EduardsBaumanis/spele/site-assets/pdf-pages/guide-01.png

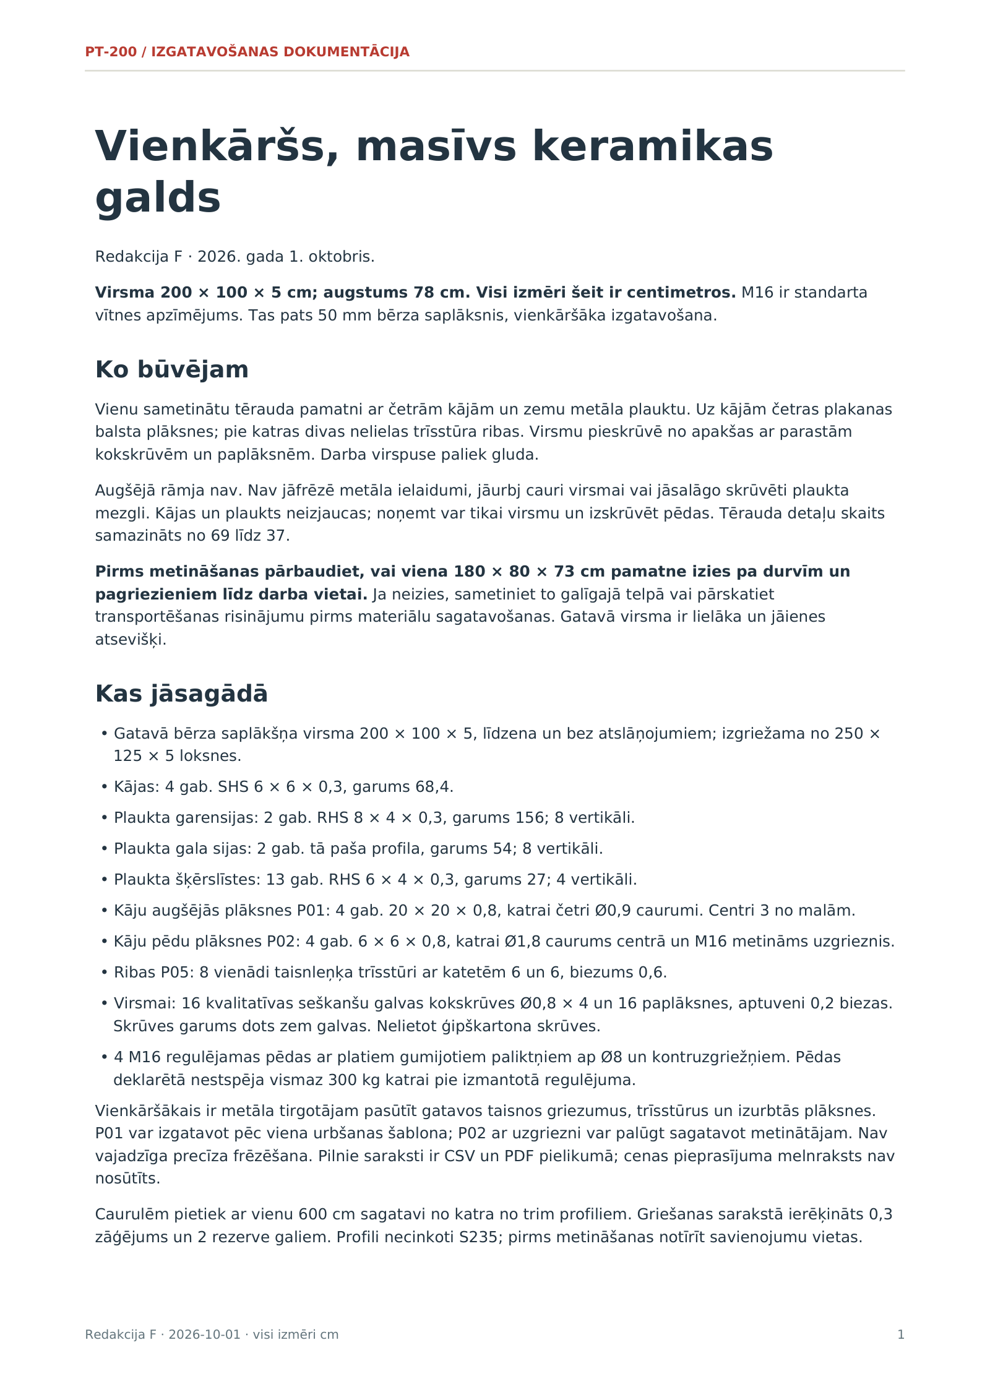
site-assets/pdf-pages/guide-01.png
