EduardsBaumanis/spele/site-assets/pdf-pages/guide-02.png

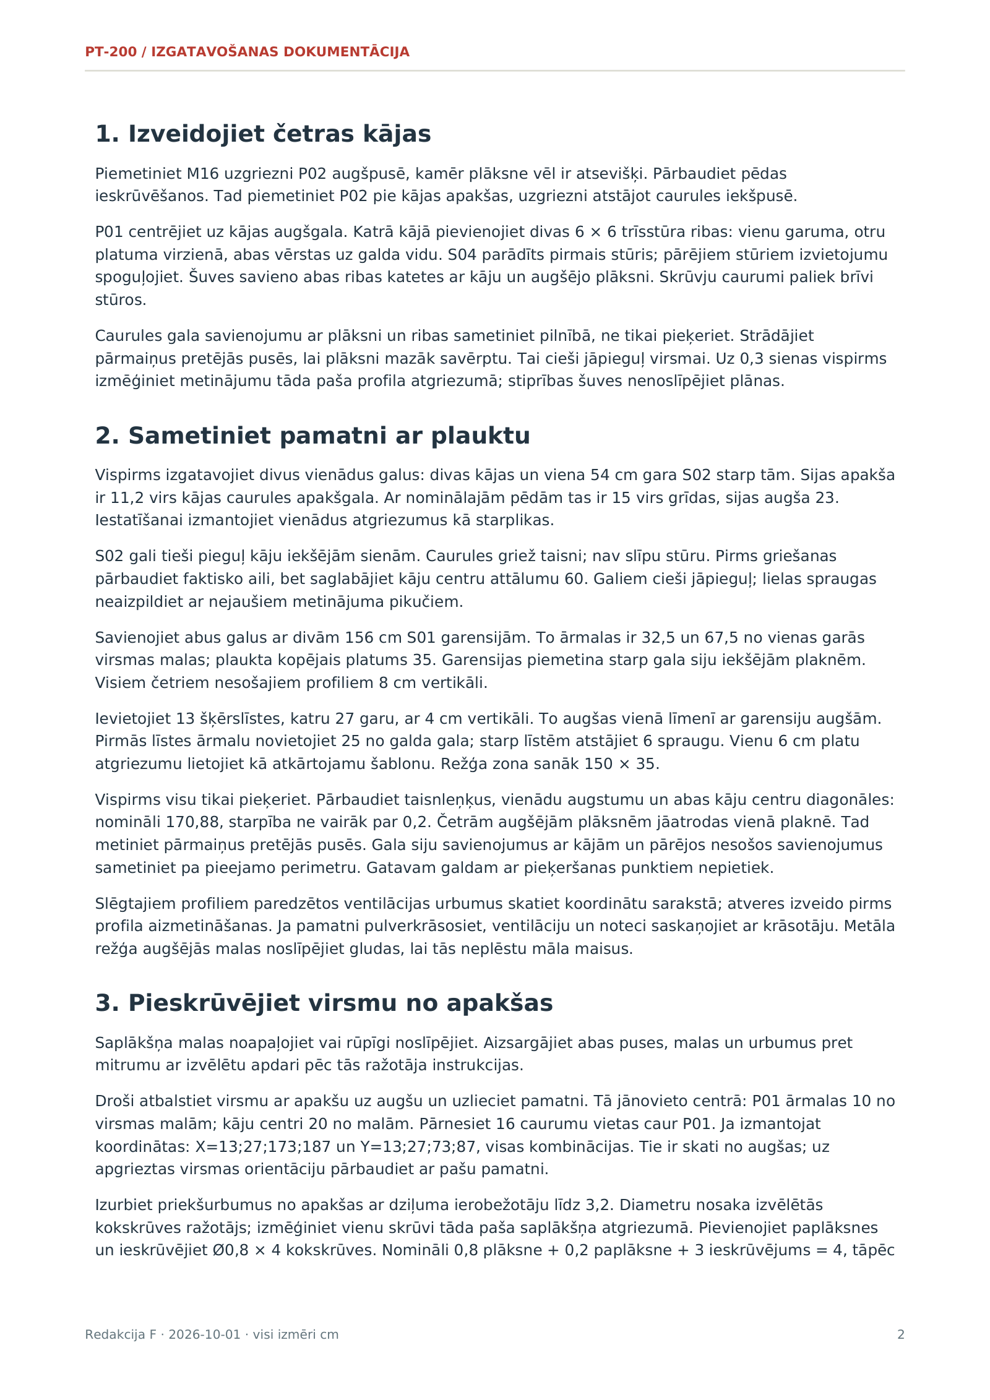
site-assets/pdf-pages/guide-02.png
