EduardsBaumanis/spele/site-assets/pdf-pages/guide-06.png

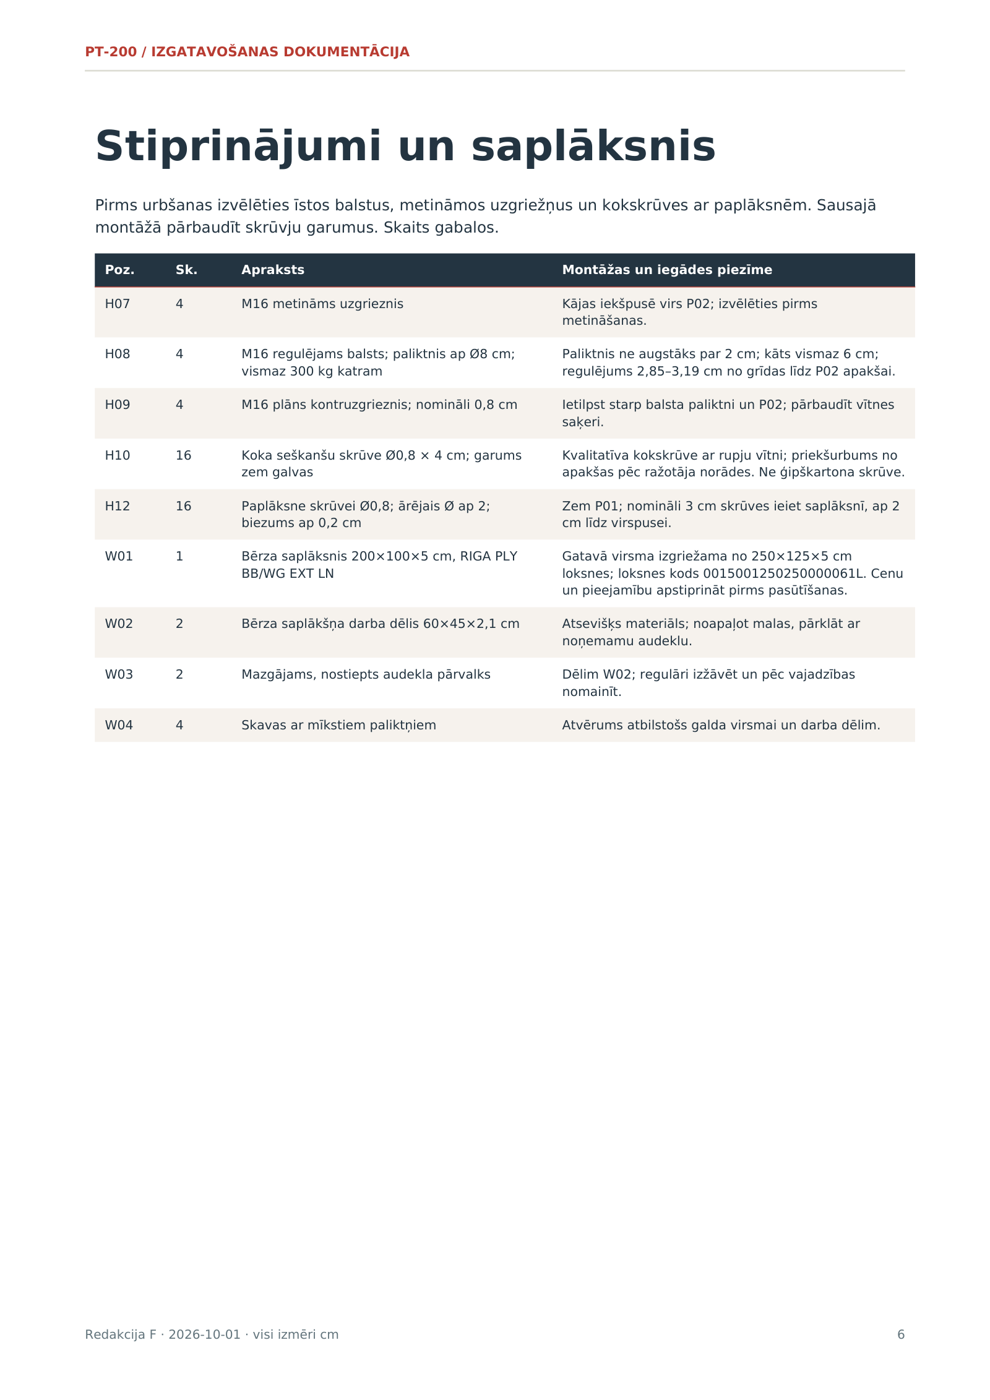
site-assets/pdf-pages/guide-06.png
