EduardsBaumanis/spele/site-assets/pdf-pages/guide-08.png

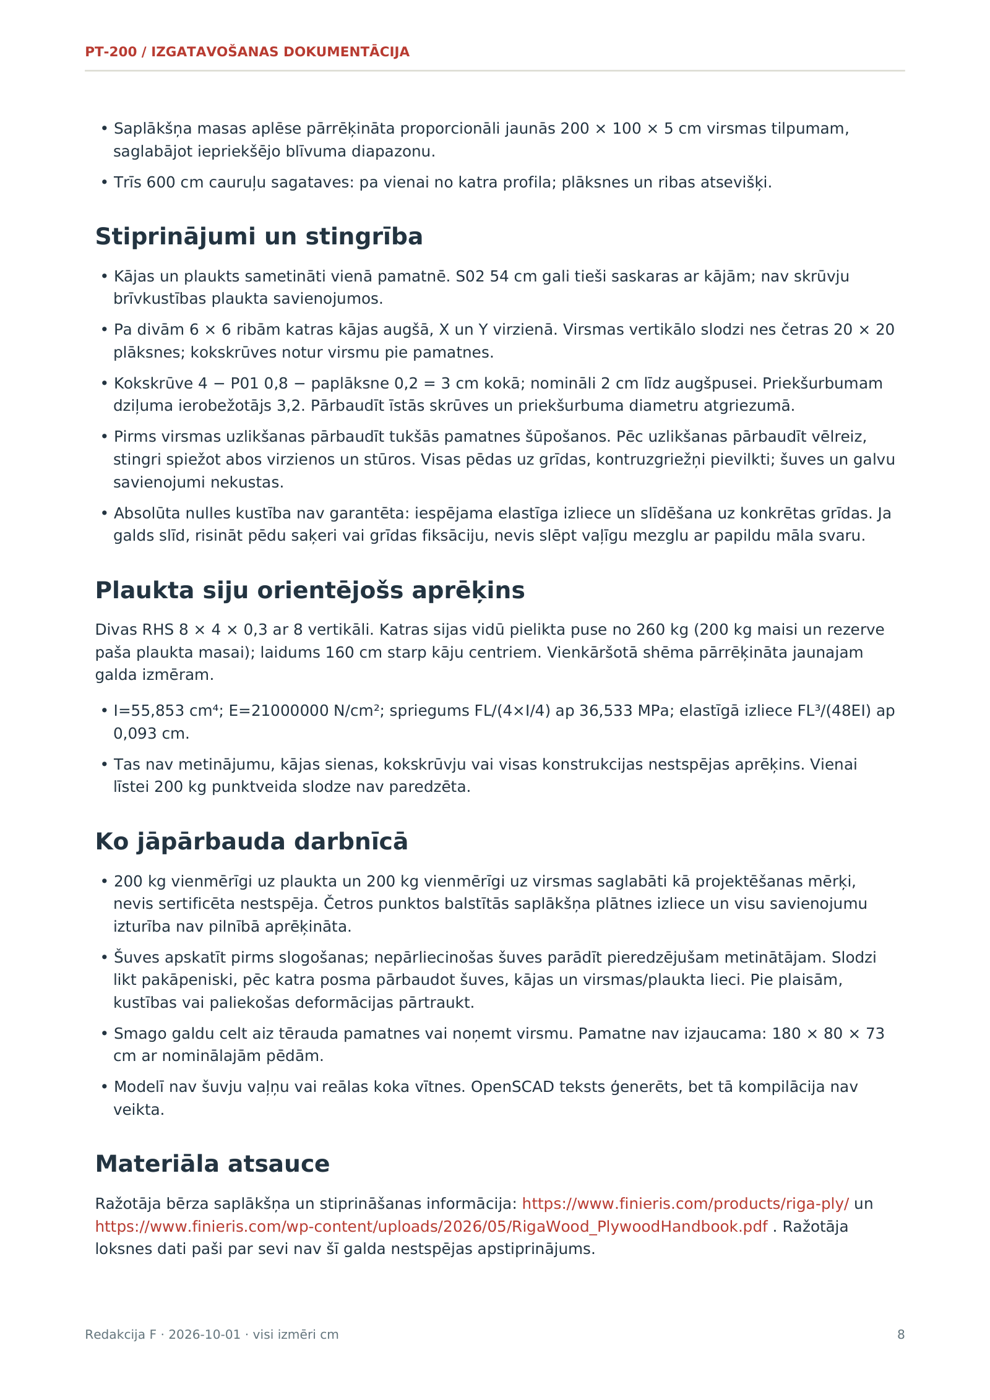
site-assets/pdf-pages/guide-08.png
